feg-giessen/VideoCtrl/software/firmware/VideoCtrl/cpp_stubs.cpp

/*
 * cpp_stubs.c
 *
 *  Created on: 08.09.2013
 *      Author: Peter Schuster
 */

#include <stdlib.h>
#include <ch.h>

void *operator new(size_t size) {
    return chHeapAlloc(NULL, size);
}

void *operator new[](size_t size) {
  return chHeapAlloc(NULL, size);
}

void operator delete(void *p) {
    chHeapFree(p);
}

void operator delete[](void *p) {
  chHeapFree(p);
}


namespace __gnu_cxx {
  void __verbose_terminate_handler() {
    chSysHalt();
  }

  extern "C" void __cxa_pure_virtual() {
    for(;;);
  }
}
