feg-giessen/VideoCtrl/software/firmware/VideoCtrl/glcd_conf.h

/*
 * glcd_conf.h
 *
 *  Created on: 31.10.2013
 *      Author: Peter Schuster
 */

#ifndef GLCD_CONF_H_
#define GLCD_CONF_H_

#define GLCD_DEVICE_CHIBIOS 		TRUE
#define GLCD_CONTROLLER_ST7565R		TRUE
#define GLCD_USE_SPI				TRUE

#endif /* GLCD_CONF_H_ */
